enderchan13/DelayTestTool/Components/LCD/lcd_image_resources.h

/* Copyright 2025 Ender Chan (Ender)
 *
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
 * You should have received a copy of the GNU General Public License
 * along with this program.  If not, see <http://www.gnu.org/licenses/>.
 */

#ifndef __LCD_IMAGE_RESOURCES_H
#define __LCD_IMAGE_RESOURCES_H

const unsigned char gImage_main_tool_name[7080] = { /* 0X00,0X10,0XB1,0X00,0X14,0X00,0X01,0X1B, */
0X00,0X00,0X00,0X00,0X02,0X08,0X02,0X10,0X03,0X10,0X03,0X10,0X03,0X10,0X03,0X10,
0X02,0X08,0X02,0X08,0X03,0X10,0X04,0X18,0X06,0X20,0X05,0X18,0X02,0X10,0X01,0X00,
0X01,0X00,0X02,0X08,0X05,0X20,0X05,0X20,0X04,0X18,0X02,0X10,0X00,0X00,0X00,0X00,
0X00,0X00,0X01,0X08,0X04,0X18,0X05,0X20,0X04,0X18,0X02,0X10,0X01,0X00,0X00,0X00,
0X00,0X00,0X00,0X00,0X00,0X00,0X01,0X00,0X03,0X10,0X04,0X18,0X06,0X20,0X05,0X18,
0X02,0X08,0X00,0X00,0X00,0X00,0X00,0X00,0X00,0X00,0X00,0X00,0X00,0X00,0X00,0X00,
0X00,0X00,0X00,0X00,0X02,0X08,0X05,0X20,0X08,0X30,0X09,0X38,0X09,0X38,0X09,0X38,
0X09,0X38,0X09,0X38,0X09,0X38,0X08,0X38,0X08,0X30,0X04,0X18,0X01,0X08,0X00,0X00,
0X00,0X00,0X00,0X00,0X00,0X00,0X00,0X00,0X02,0X08,0X04,0X18,0X05,0X20,0X05,0X20,
0X02,0X08,0X01,0X08,0X01,0X08,0X02,0X08,0X02,0X10,0X02,0X08,0X00,0X00,0X00,0X00,
0X02,0X08,0X03,0X10,0X05,0X20,0X05,0X20,0X02,0X10,0X01,0X00,0X00,0X00,0X00,0X00,
0X00,0X00,0X00,0X00,0X01,0X00,0X02,0X08,0X03,0X10,0X04,0X18,0X04,0X18,0X04,0X18,
0X04,0X18,0X03,0X10,0X02,0X08,0X02,0X08,0X05,0X20,0X07,0X30,0X08,0X38,0X08,0X30,
0X06,0X20,0X02,0X08,0X01,0X08,0X00,0X00,0X00,0X00,0X00,0X00,0X00,0X00,0X00,0X00,
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
0X00,0X08,0X00,0X10,0X67,0X9A,0X29,0XD3,0X29,0XDB,0X4A,0XCB,0X20,0X28,0X00,0X18,
0X40,0X40,0X40,0X60,0X40,0X60,0X60,0X50,0X00,0X18,0X00,0X08,0X00,0X08,0X00,0X18,
0X60,0X50,0X20,0X60,0X40,0X60,0X40,0X40,0X00,0X18,0X00,0X08,0X00,0X10,0X20,0X48,
0X20,0X60,0X20,0X68,0X40,0X58,0X00,0X18,};
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
